dpavlin/dc2025badge/firmware/Core/Inc/main.h

#define BUTTON0_Pin GPIO_PIN_0
#define BUTTON0_GPIO_Port GPIOC
#define BUTTON0_EXTI_IRQn EXTI0_1_IRQn
#define BUTTON1ALT_Pin GPIO_PIN_1
#define BUTTON1ALT_GPIO_Port GPIOC
#define BUTTON1ALT_EXTI_IRQn EXTI0_1_IRQn
#define BUTTON1_Pin GPIO_PIN_2
#define BUTTON1_GPIO_Port GPIOC
#define BUTTON1_EXTI_IRQn EXTI2_3_IRQn
#define NFC_BSS_Pin GPIO_PIN_3
#define NFC_BSS_GPIO_Port GPIOA
#define NFC_IRQ_Pin GPIO_PIN_4
#define NFC_IRQ_GPIO_Port GPIOA
#define NFC_IRQ_EXTI_IRQn EXTI4_15_IRQn
#define LED_NINT_Pin GPIO_PIN_8
#define LED_NINT_GPIO_Port GPIOB
#define LED_NINT_EXTI_IRQn EXTI4_15_IRQn
#define LED_NSD_Pin GPIO_PIN_9
#define LED_NSD_GPIO_Port GPIOB
